yoshiko-kulala/enc2uart/src/encoder_test/Core/Src/main.c

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
/* Includes ------------------------------------------------------------------*/
#include "main.h"

/* USER CODE BEGIN Includes */
#include "xprintf.h"
/* USER CODE END Includes */

TIM_HandleTypeDef htim1;
TIM_HandleTypeDef htim2;
TIM_HandleTypeDef htim3;
TIM_HandleTypeDef htim4;
TIM_HandleTypeDef htim10;

UART_HandleTypeDef huart2;
UART_HandleTypeDef huart6;

void SystemClock_Config(void);
static void MX_GPIO_Init(void);
static void MX_USART2_UART_Init(void);
static void MX_TIM3_Init(void);
static void MX_TIM1_Init(void);
static void MX_TIM2_Init(void);
static void MX_TIM4_Init(void);
static void MX_TIM10_Init(void);
static void MX_USART6_UART_Init(void);
/* USER CODE BEGIN 0 */
float pwm[4] = { 0 };
void Count2rpm() {
	pwm[0] = TIM1->CNT - 30000;
	pwm[1] = TIM2->CNT - 30000;
	pwm[2] = TIM3->CNT - 30000;
	pwm[3] = TIM4->CNT - 30000;
	TIM1->CNT = 30000;
	TIM2->CNT = 30000;
	TIM3->CNT = 30000;
	TIM4->CNT = 30000;
}

void uart_putc(uint8_t c) {
	char buf[1];
	buf[0] = c;
	HAL_UART_Transmit(&huart2, (uint8_t*) buf, sizeof(buf), 0xFFFF);
}
void uart_puts(char *str) {
	while (*str) {
		uart_putc(*str++);
	}
}

TIM_Encoder_InitTypeDef sConfig1;
TIM_Encoder_InitTypeDef sConfig2;
TIM_Encoder_InitTypeDef sConfig3;
TIM_Encoder_InitTypeDef sConfig4;
TIM_MasterConfigTypeDef sMasterConfig1;
TIM_MasterConfigTypeDef sMasterConfig2;
TIM_MasterConfigTypeDef sMasterConfig3;
TIM_MasterConfigTypeDef sMasterConfig4;
/* USER CODE END 0 */

/**
  * @brief  The application entry point.
  * @retval int
  */
int main(void)
{
  /* USER CODE BEGIN 1 */
	xdev_out(uart_putc);

  /* USER CODE END 1 */

  /* MCU Configuration--------------------------------------------------------*/

  /* Reset of all peripherals, Initializes the Flash interface and the Systick. */
  HAL_Init();

  /* Configure the system clock */
  SystemClock_Config();

  /* Initialize all configured peripherals */
  MX_GPIO_Init();
  MX_USART2_UART_Init();
  MX_TIM3_Init();
  MX_TIM1_Init();
  MX_TIM2_Init();
  MX_TIM4_Init();
  MX_TIM10_Init();
  MX_USART6_UART_Init();
  /* USER CODE BEGIN 2 */
	uint8_t buf[5];
	uint16_t tx_rpm[4] = { 500, 500, 500, 500 };
	if (HAL_TIM_Encoder_Init(&htim1, &sConfig1) != HAL_OK) {
		Error_Handler();
	}
	HAL_TIM_Encoder_Start(&htim1, TIM_CHANNEL_ALL);
	TIM1->CNT = 30000;

	if (HAL_TIM_Encoder_Init(&htim2, &sConfig2) != HAL_OK) {
		Error_Handler();
	}
	HAL_TIM_Encoder_Start(&htim2, TIM_CHANNEL_ALL);
	TIM2->CNT = 30000;

	if (HAL_TIM_Encoder_Init(&htim3, &sConfig3) != HAL_OK) {
		Error_Handler();
	}
	HAL_TIM_Encoder_Start(&htim3, TIM_CHANNEL_ALL);
	TIM3->CNT = 30000;

	if (HAL_TIM_Encoder_Init(&htim4, &sConfig4) != HAL_OK) {
		Error_Handler();
	}
	HAL_TIM_Encoder_Start(&htim4, TIM_CHANNEL_ALL);
	TIM4->CNT = 30000;
	HAL_TIM_Base_Start_IT(&htim10);
  /* USER CODE END 2 */

  /* Infinite loop */
  /* USER CODE BEGIN WHILE */
	while (1) {
		for (int i = 0; i < 4; i++) {
			tx_rpm[i] = (int)pwm[i] + 500;
		}
		buf[0] = (tx_rpm[0] & 0xFF);
		buf[1] = (((tx_rpm[0] >> 8) + (tx_rpm[1] << 2)) & 0xFF);
		buf[2] = (((tx_rpm[1] >> 6) + (tx_rpm[2] << 4)) & 0xFF);
		buf[3] = (((tx_rpm[2] >> 4) + (tx_rpm[3] << 6)) & 0xFF);
		buf[4] = ((tx_rpm[3] >> 2) & 0xFF);
		HAL_UART_Transmit(&huart6, buf, sizeof(buf), 0xFFFF);
		xprintf("%d,%d,%d,%d\r\n",(int)pwm[0],(int)pwm[1],(int)pwm[2],(int)pwm[3]);
		HAL_Delay(100);
    /* USER CODE END WHILE */

    /* USER CODE BEGIN 3 */
	}
  /* USER CODE END 3 */
}

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
